tiberiuonichi/Discrete-Square-Wave-Generator/Simulation/DC_Current_Bias_Points.jpg

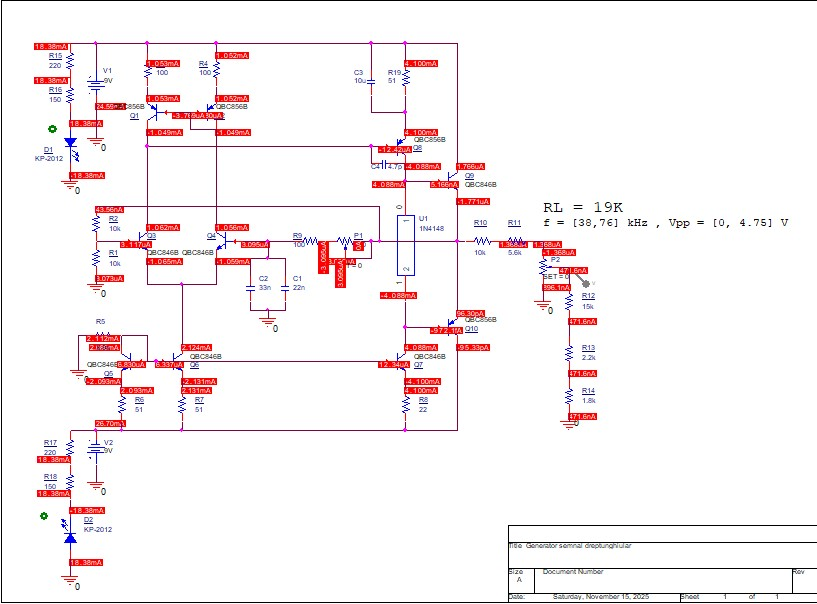
Simulation/DC_Current_Bias_Points.jpg
