tiberiuonichi/Discrete-Square-Wave-Generator/Simulation/DC_Voltage_Bias_Points.jpg

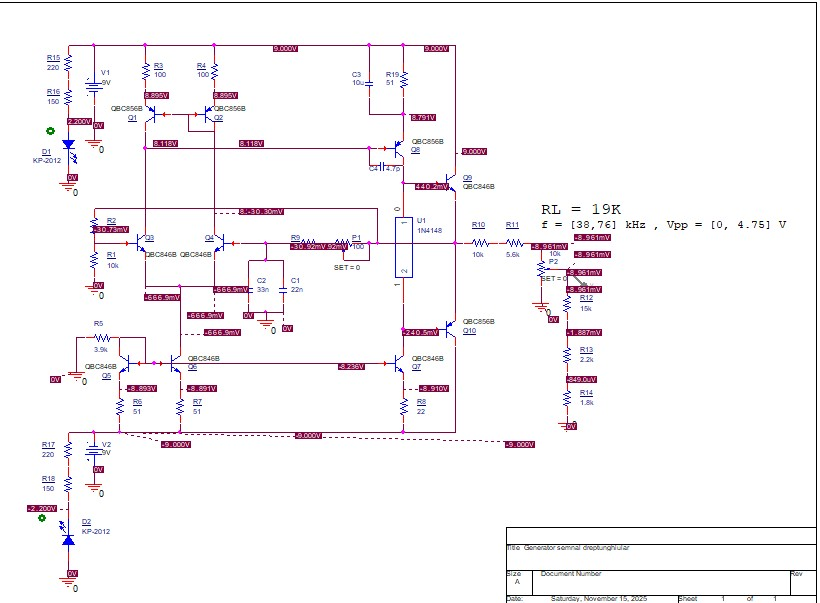
Simulation/DC_Voltage_Bias_Points.jpg
