tiberiuonichi/Discrete-Square-Wave-Generator/Simulation/Maximum_Frequency.jpg

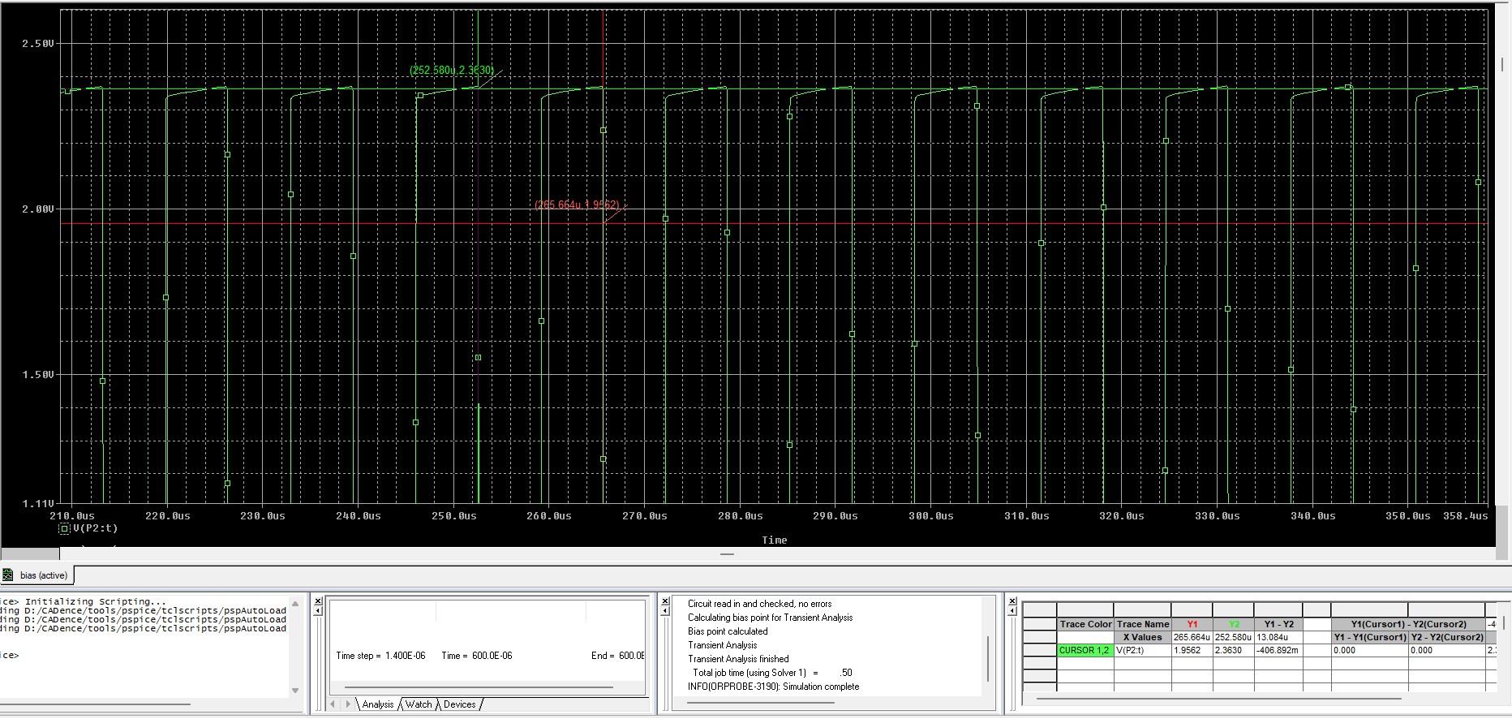
Simulation/Maximum_Frequency.jpg
