tiberiuonichi/Discrete-Square-Wave-Generator/Simulation/Maximum_Peak-to-Peak_Voltage.jpg

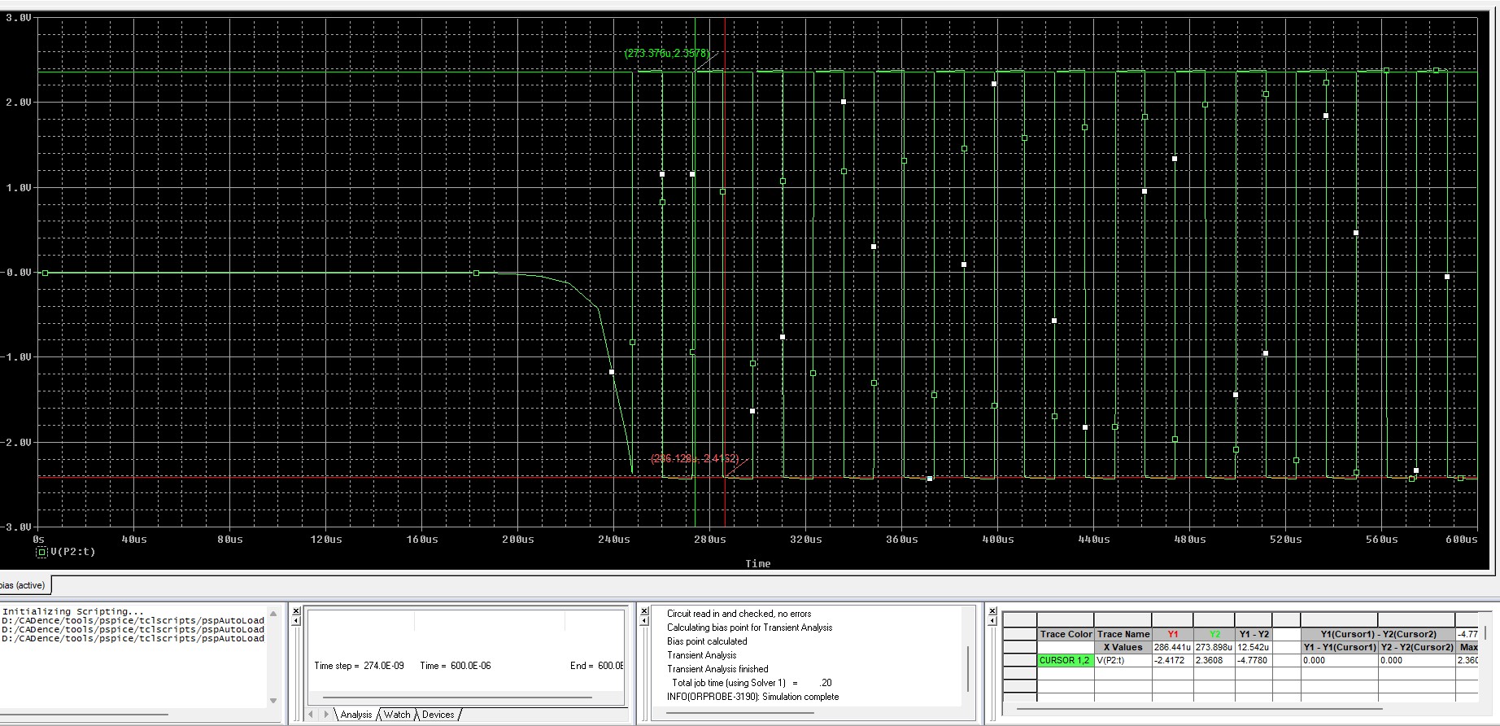
Simulation/Maximum_Peak-to-Peak_Voltage.jpg
