tiberiuonichi/Discrete-Square-Wave-Generator/Simulation/Minimum_Frequency.jpg

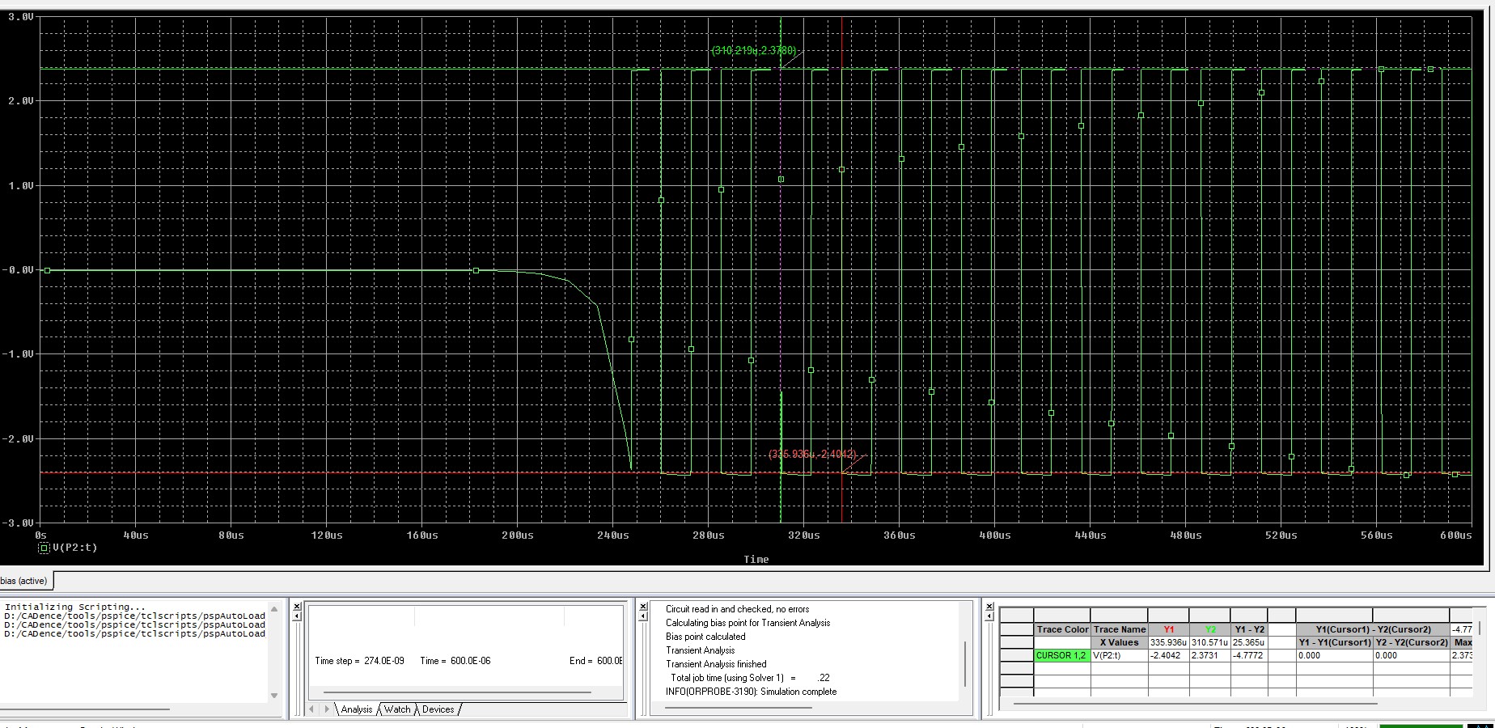
Simulation/Minimum_Frequency.jpg
